RobertFach/panobot/model/Case_for_the_Full_Graphic_Smart_LCD_Controller/images/a5eb6d9422914732d463301576c6b438_preview_featured.jpg

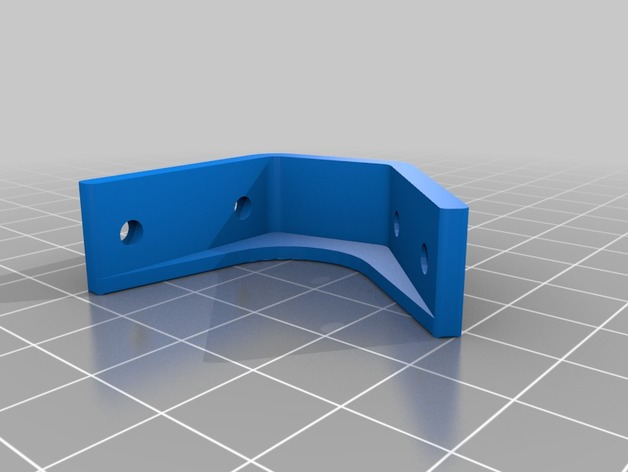
model/Case_for_the_Full_Graphic_Smart_LCD_Controller/images/a5eb6d9422914732d463301576c6b438_preview_featured.jpg
