RobertFach/panobot/model/Case_for_the_Full_Graphic_Smart_LCD_Controller/images/Bottom_Case_FGD-_pockets_preview_featured.jpg

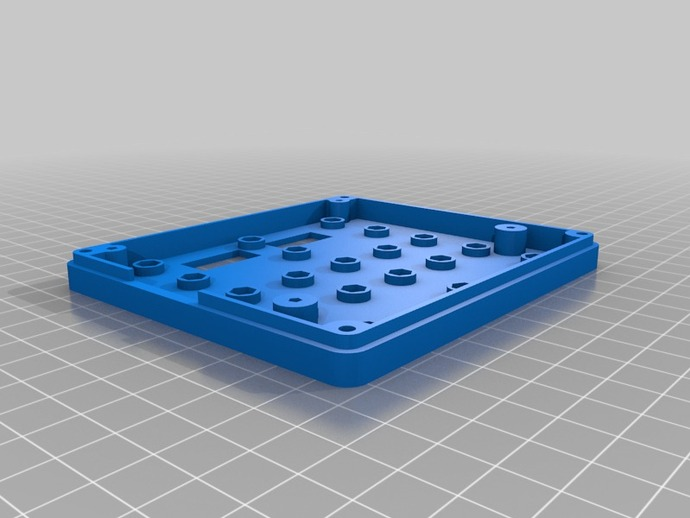
model/Case_for_the_Full_Graphic_Smart_LCD_Controller/images/Bottom_Case_FGD-_pockets_preview_featured.jpg
