RobertFach/panobot/model/Case_for_the_Full_Graphic_Smart_LCD_Controller/images/green_display_large2_preview_featured.jpg

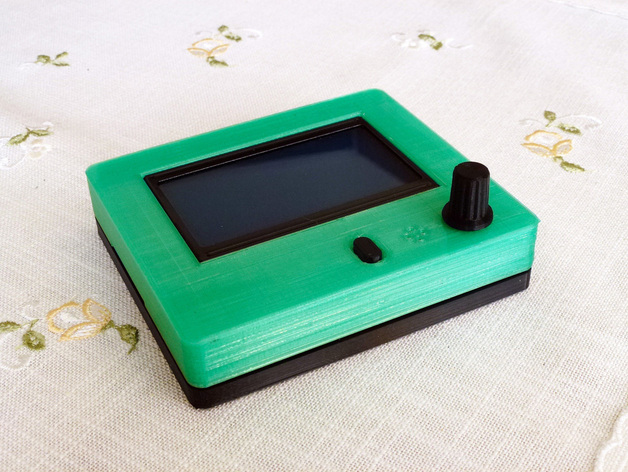
model/Case_for_the_Full_Graphic_Smart_LCD_Controller/images/green_display_large2_preview_featured.jpg
