RobertFach/panobot/model/Case_for_the_Full_Graphic_Smart_LCD_Controller/images/Kill_Button_FGD_preview_featured.jpg

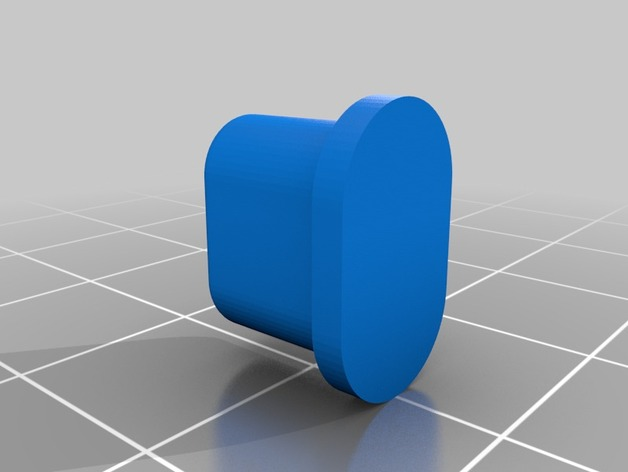
model/Case_for_the_Full_Graphic_Smart_LCD_Controller/images/Kill_Button_FGD_preview_featured.jpg
