RobertFach/panobot/pcb/CameraBot-PCB-BACK.png

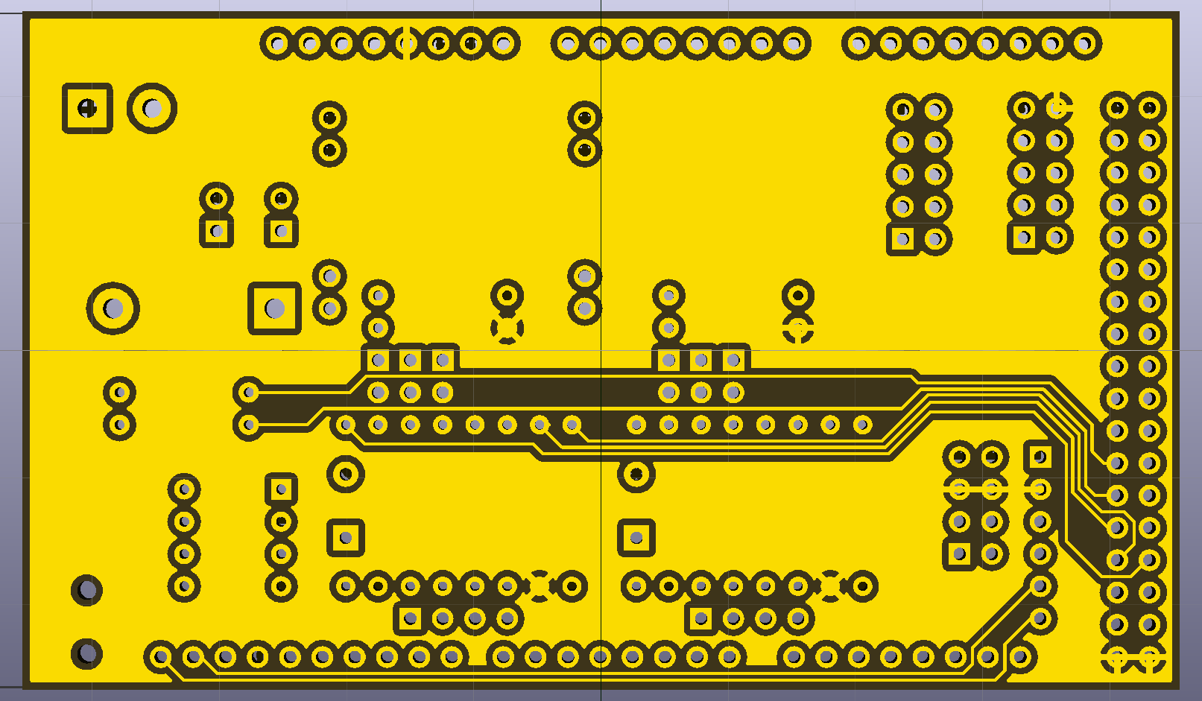
pcb/CameraBot-PCB-BACK.png
