RobertFach/panobot/pcb/CameraBot-PCB-FRONT.png

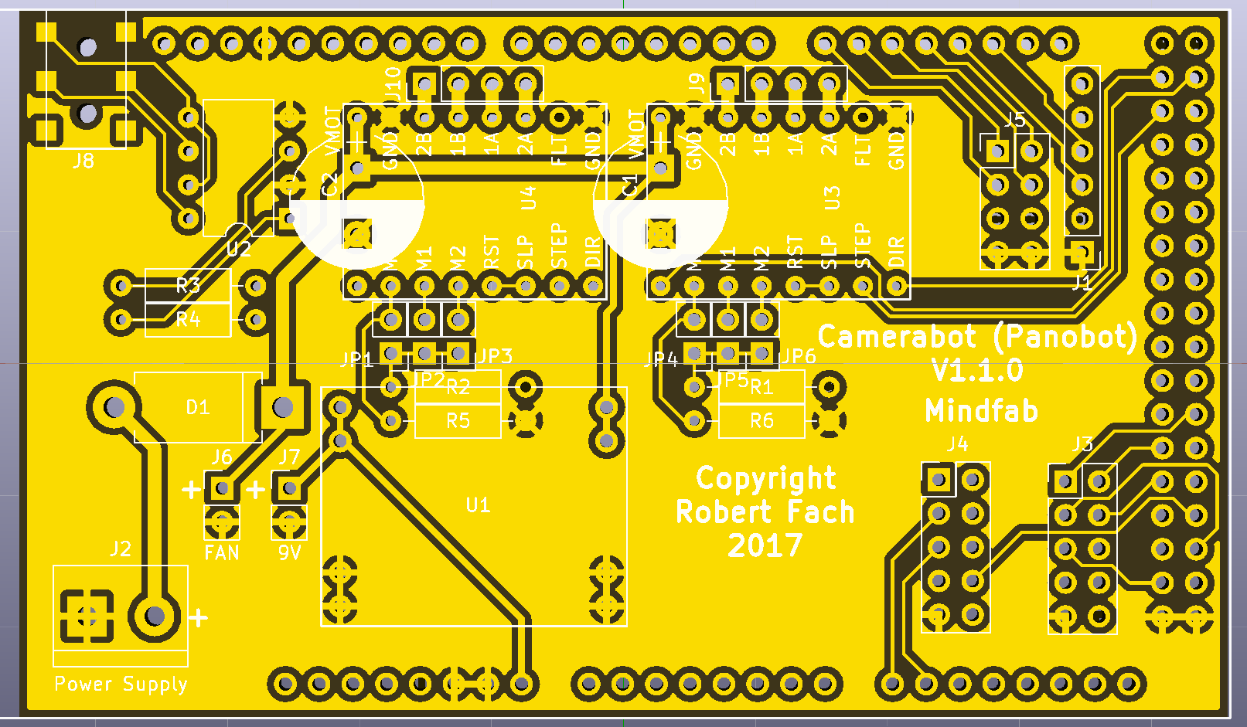
pcb/CameraBot-PCB-FRONT.png
