RobertFach/panobot/wiki/images/pcb-backside-complete.JPG

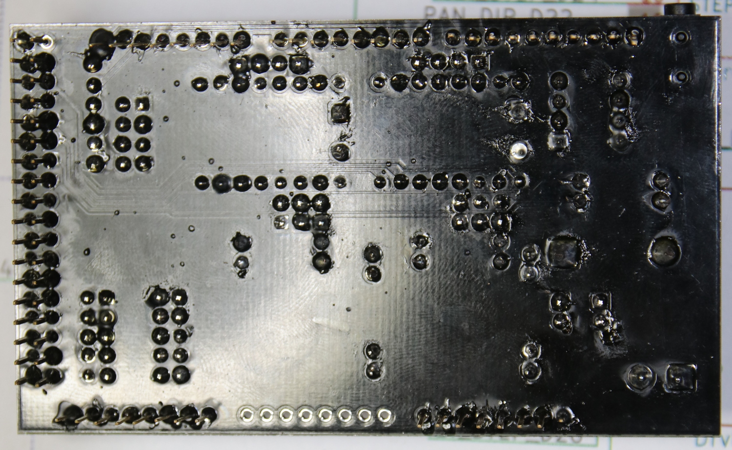
wiki/images/pcb-backside-complete.JPG
