RobertFach/panobot/wiki/images/pcb-complete-1.JPG

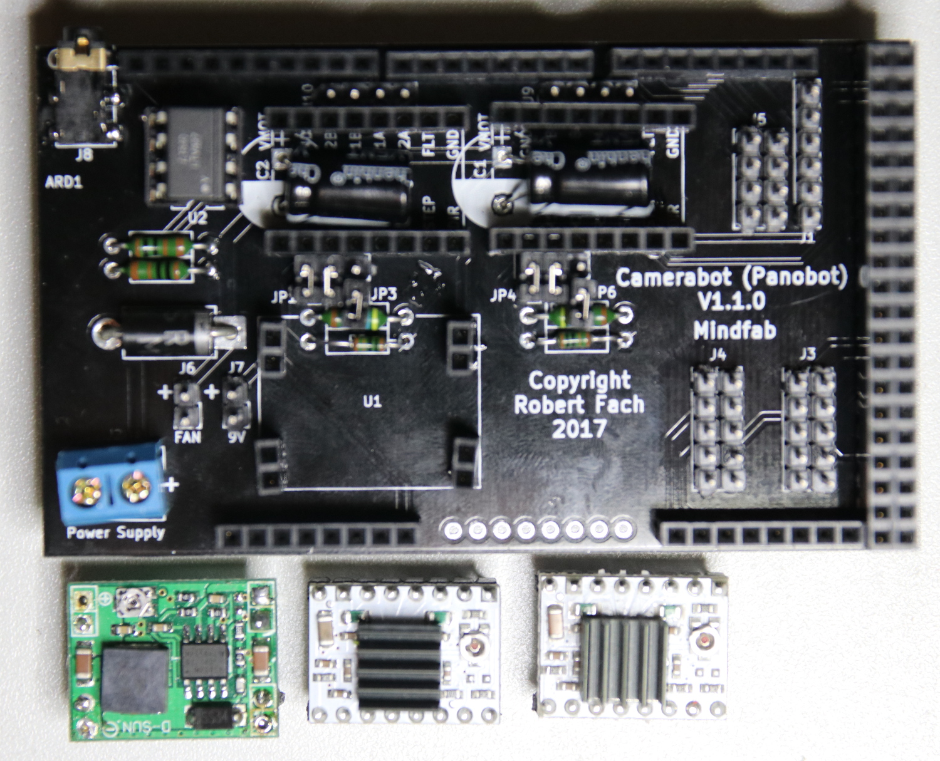
wiki/images/pcb-complete-1.JPG
