RobertFach/panobot/wiki/images/pcb-complete.JPG

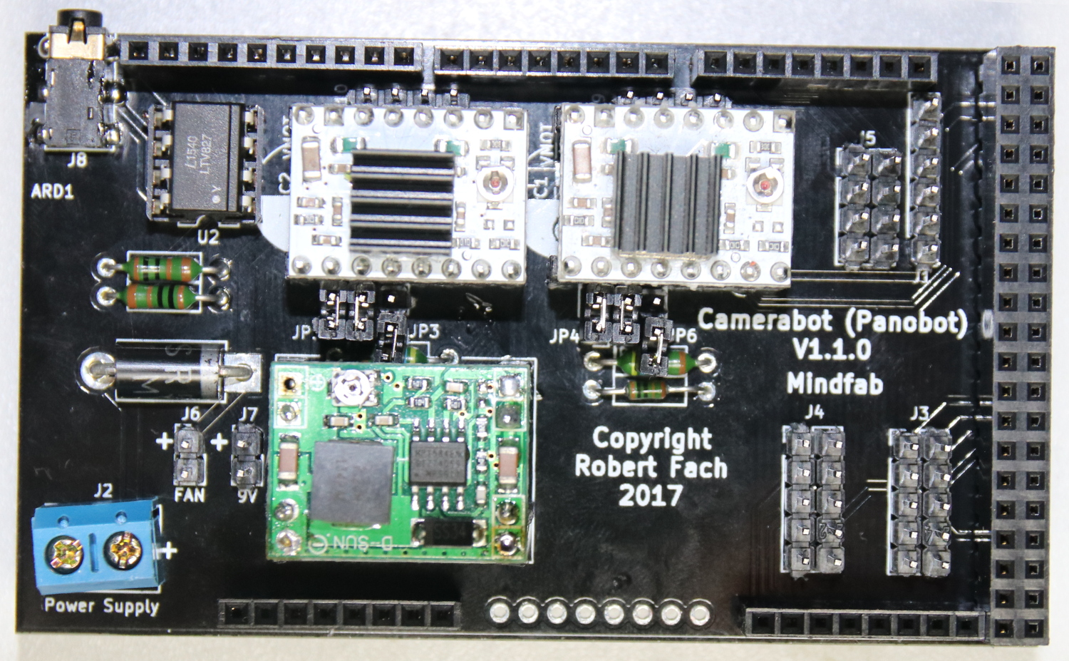
wiki/images/pcb-complete.JPG
