RobertFach/panobot/wiki/images/pcb-front.JPG

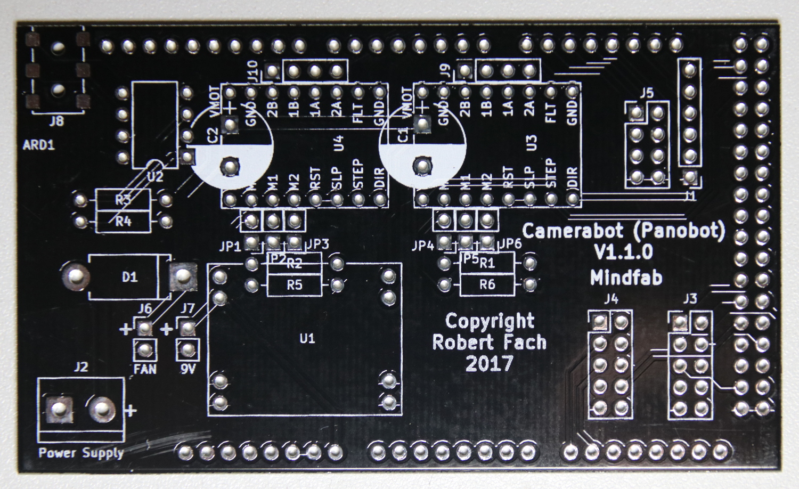
wiki/images/pcb-front.JPG
