RobertFach/panobot/model/tiltsteppermount.stl

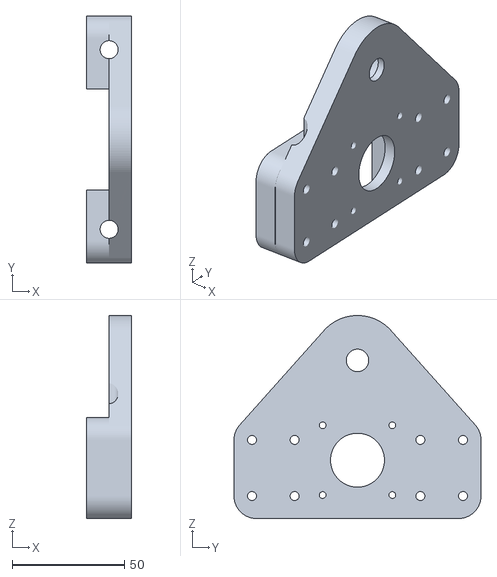
[picture p36: CAD file, 2017-07-06]
model/tiltsteppermount.stl
20.1 x 110.0 x 90.4
