RobertFach/panobot/model/Case_for_the_Full_Graphic_Smart_LCD_Controller/files/Spacer_FGD.stl

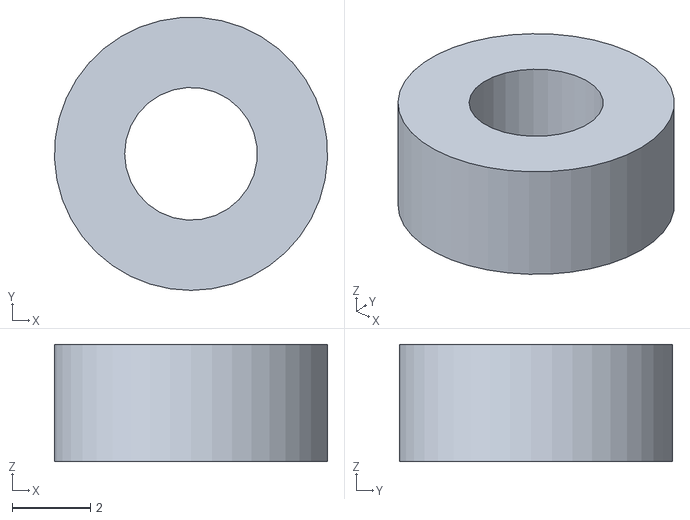
[picture p37: CAD file, 2017-09-01]
model/Case_for_the_Full_Graphic_Smart_LCD_Controller/files/Spacer_FGD.stl
6.99 x 6.99 x 3.00
