RobertFach/panobot/model/print/quickmountclamp.stl

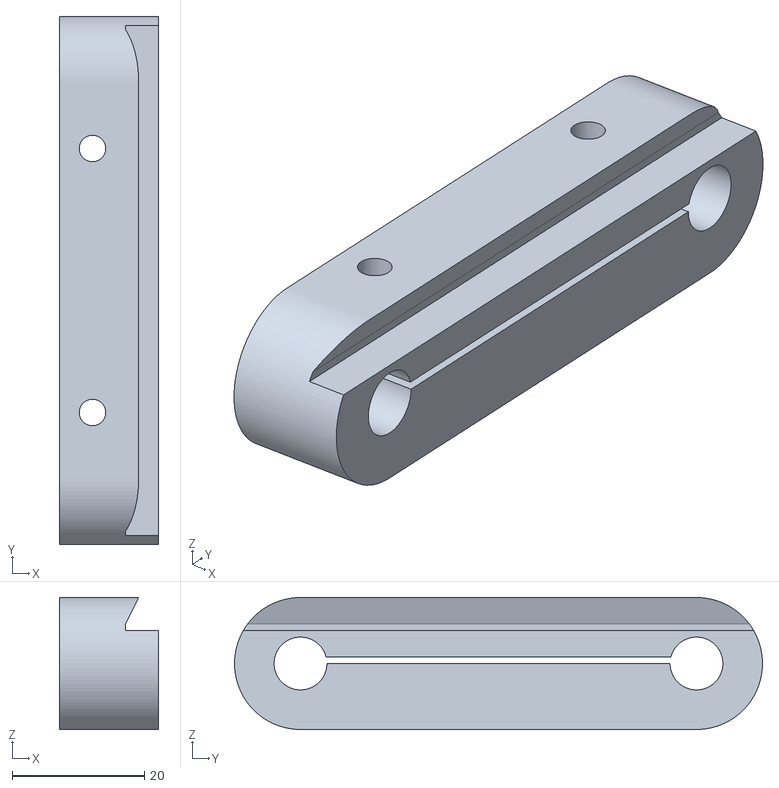
[picture p38: CAD file, 2017-07-07]
model/print/quickmountclamp.stl
15.0 x 80.0 x 20.0
