RobertFach/panobot/model/stepper_pan_mount.stl

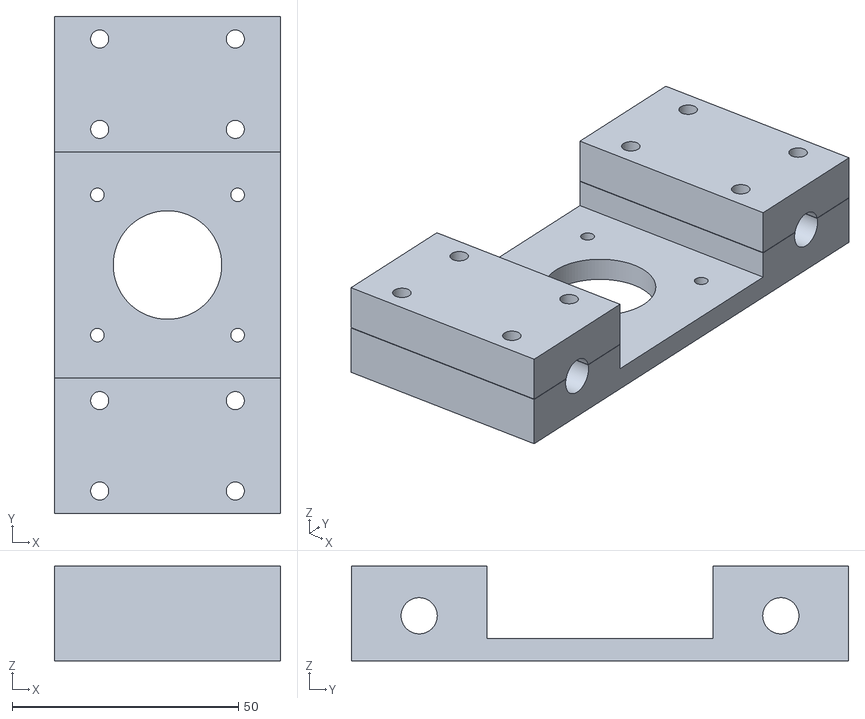
[picture p39: CAD file, 2017-07-06]
model/stepper_pan_mount.stl
50.0 x 110.0 x 21.0
