RobertFach/panobot/model/Case_for_the_Full_Graphic_Smart_LCD_Controller/files/Case_Clamp.stl

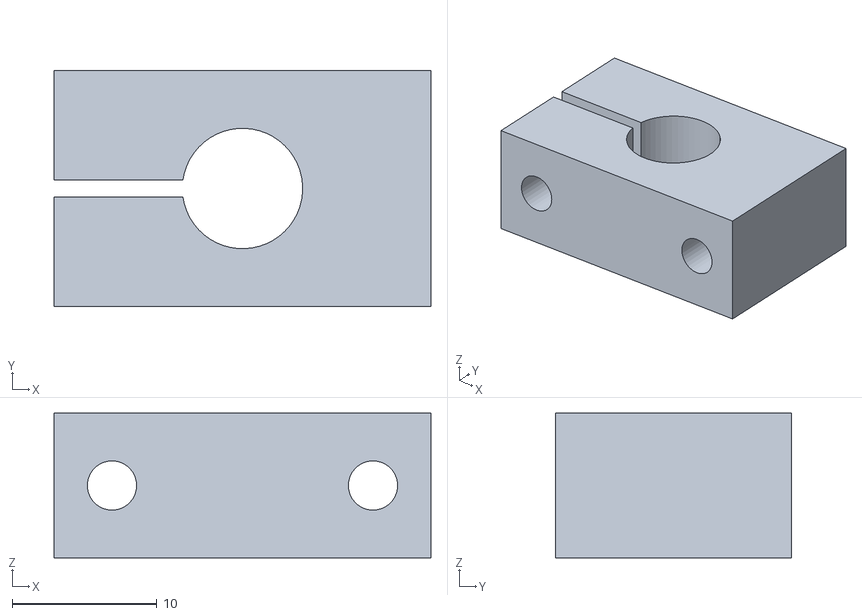
[picture p40: CAD file, 2017-09-01]
model/Case_for_the_Full_Graphic_Smart_LCD_Controller/files/Case_Clamp.stl
26.0 x 16.3 x 10.0
