RobertFach/panobot/model/central_pan.stl

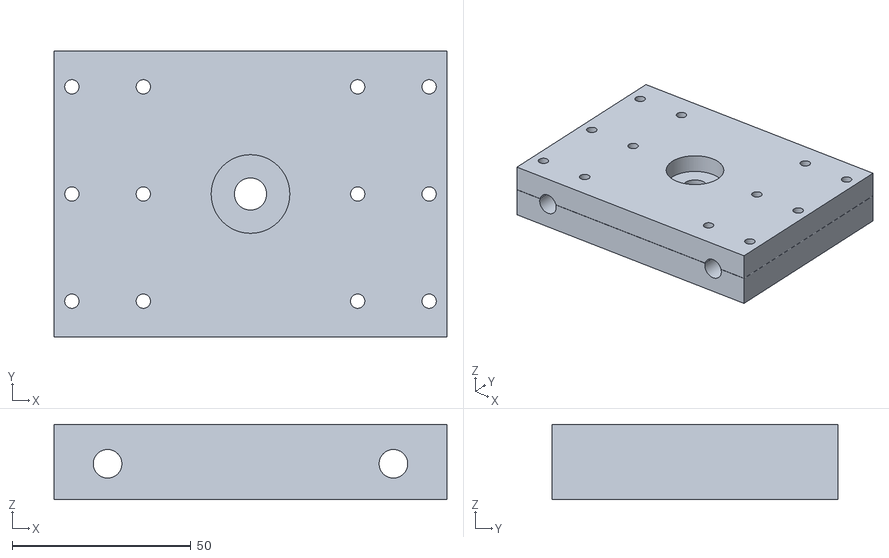
[picture p41: CAD file, 2017-07-06]
model/central_pan.stl
110.0 x 80.0 x 21.0
