RobertFach/panobot/model/print/camquickmount.stl

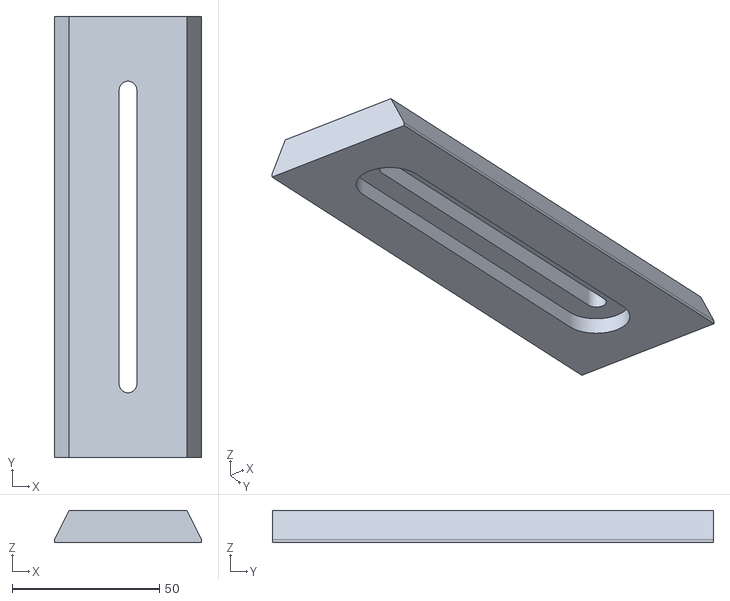
[picture p42: CAD file, 2017-07-07]
model/print/camquickmount.stl
50.0 x 150.0 x 11.0
