RobertFach/panobot/model/Case_for_the_Full_Graphic_Smart_LCD_Controller/files/Top_Case_FGD.stl

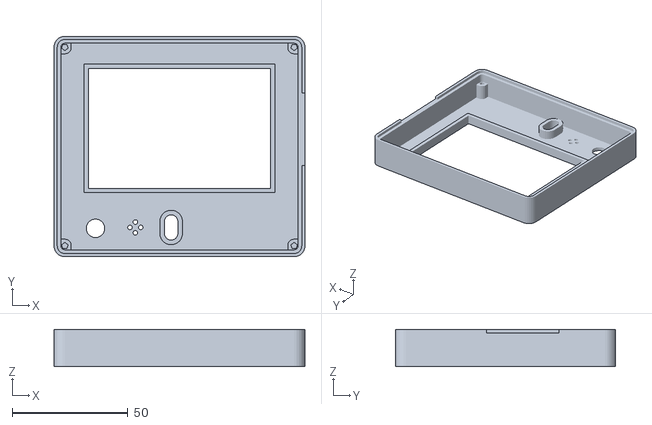
[picture p43: CAD file, 2017-09-01]
model/Case_for_the_Full_Graphic_Smart_LCD_Controller/files/Top_Case_FGD.stl
108.6 x 95.4 x 16.1
