RobertFach/panobot/model/pantiltconnector.stl

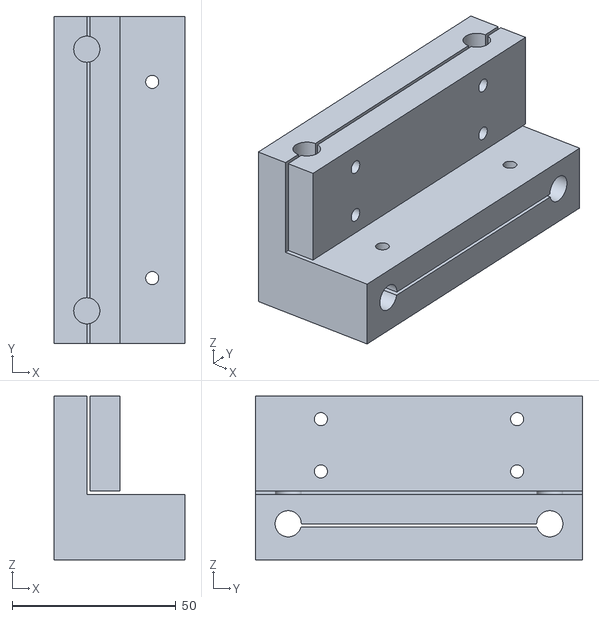
[picture p44: CAD file, 2017-07-06]
model/pantiltconnector.stl
40.0 x 100.0 x 50.0
