RobertFach/panobot/model/print/tiltsidedrive.stl

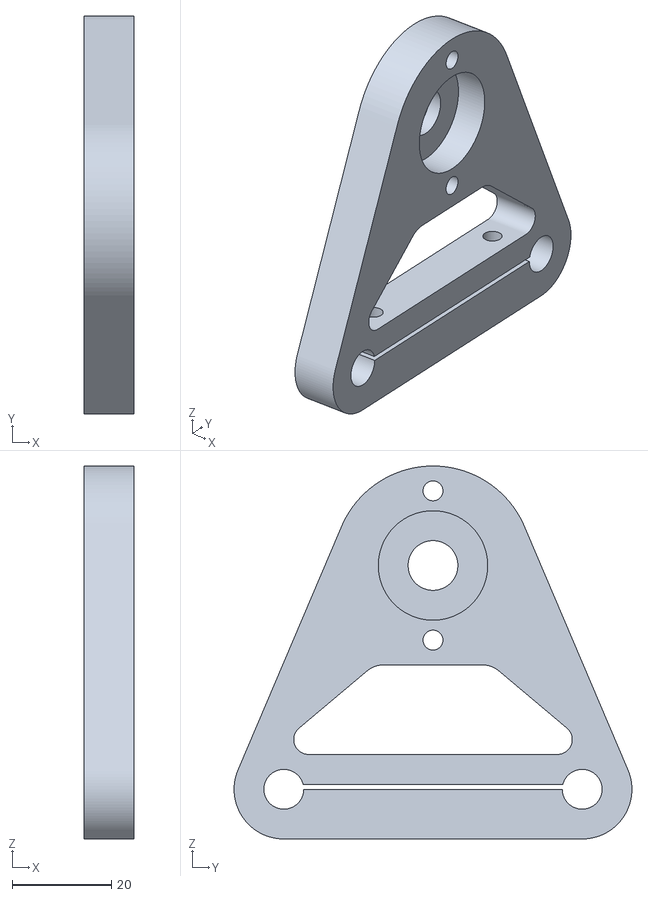
[picture p45: CAD file, 2017-07-06]
model/print/tiltsidedrive.stl
10.0 x 80.0 x 75.0
