RobertFach/panobot/model/gigascan.stl

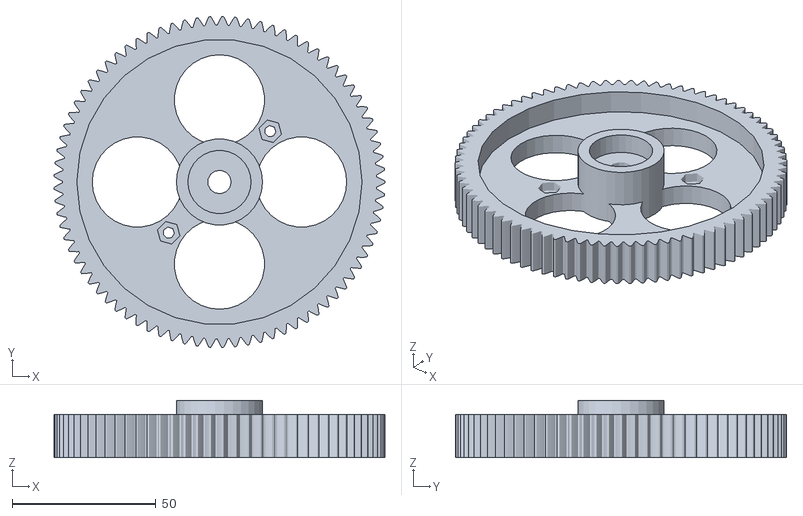
[picture p46: CAD file, 2017-07-06]
model/gigascan.stl
115.2 x 115.3 x 20.0
