RobertFach/panobot/model/print/tiltsidedrivegear.stl

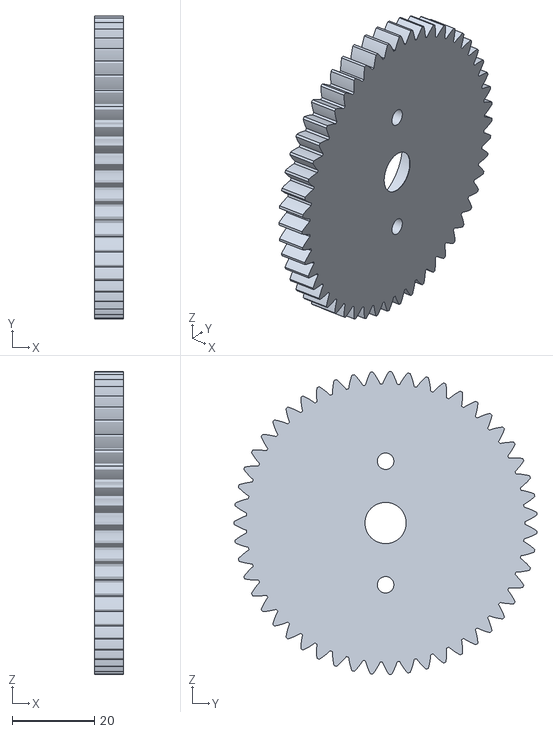
[picture p47: CAD file, 2017-07-06]
model/print/tiltsidedrivegear.stl
7.00 x 73.6 x 73.6
