RobertFach/panobot/model/print/drivegear.stl

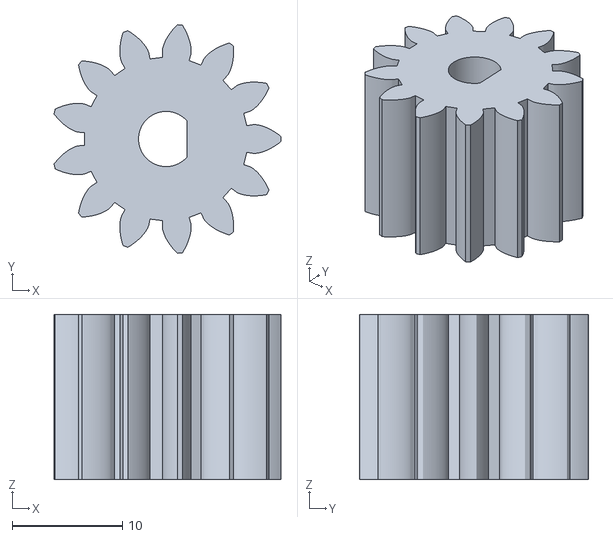
[picture p48: CAD file, 2017-07-06]
model/print/drivegear.stl
20.6 x 20.7 x 15.0
