RobertFach/panobot/model/print/central_gear.stl

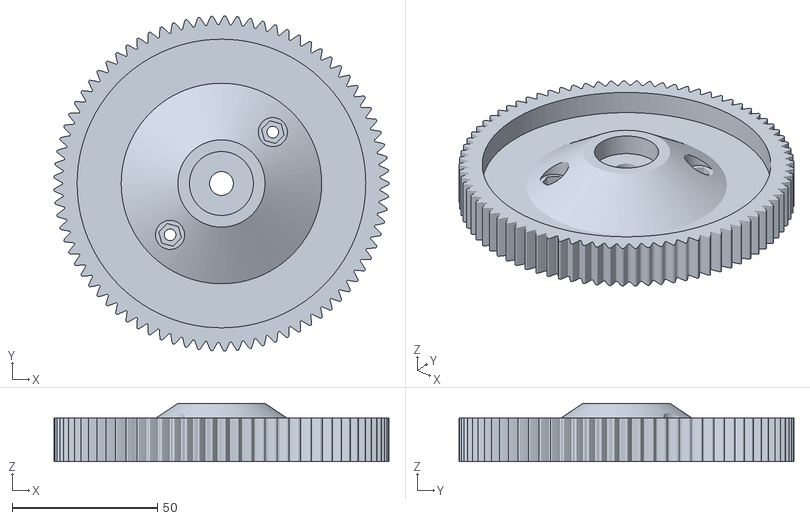
[picture p49: CAD file, 2017-07-06]
model/print/central_gear.stl
115.2 x 115.3 x 20.0
